mplinuxgeek/ESPmmWave-LD2450/images/PXL_20250126_034155016.jpg

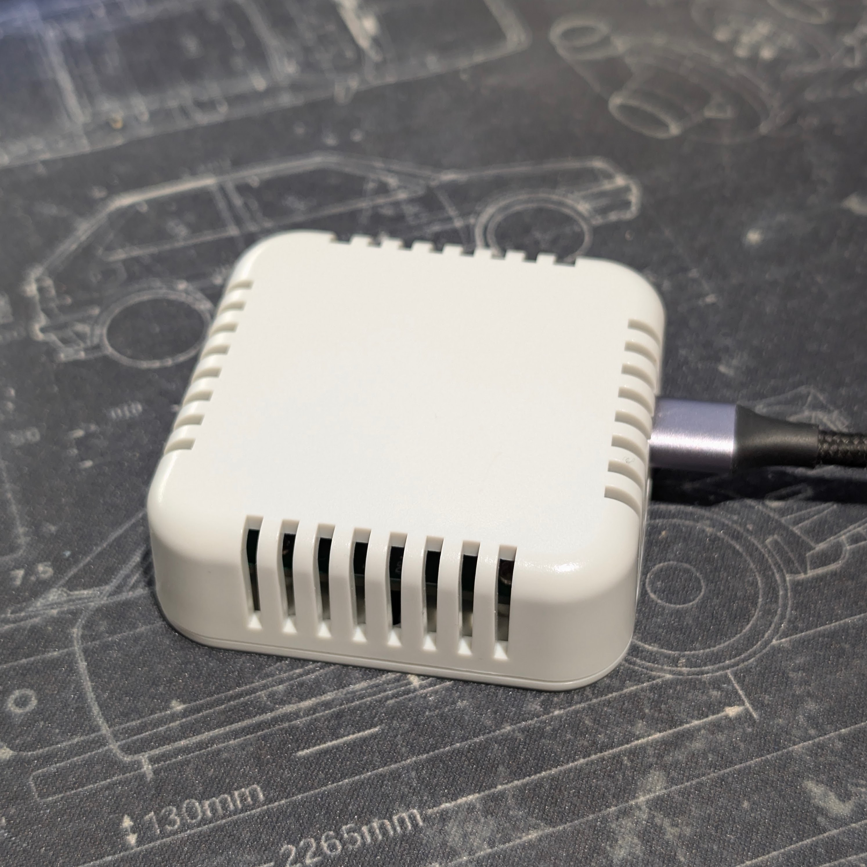
images/PXL_20250126_034155016.jpg
